xoquox/esp8266-sesam/static.h

const PROGMEM char static_index_html[] = {
  0x20, 0x3c, 0x21, 0x44, 0x4f, 0x43, 0x54, 0x59, 0x50, 0x45, 0x20, 0x68,
  0x74, 0x6d, 0x6c, 0x3e, 0x0a, 0x20, 0x3c, 0x68, 0x74, 0x6d, 0x6c, 0x20,
  0x6c, 0x61, 0x6e, 0x67, 0x3d, 0x22, 0x65, 0x6e, 0x22, 0x3e, 0x0a, 0x20,
  0x3c, 0x68, 0x65, 0x61, 0x64, 0x3e, 0x0a, 0x20, 0x3c, 0x6d, 0x65, 0x74,
  0x61, 0x20, 0x63, 0x68, 0x61, 0x72, 0x73, 0x65, 0x74, 0x3d, 0x22, 0x75,
  0x74, 0x66, 0x2d, 0x38, 0x22, 0x3e, 0x0a, 0x20, 0x3c, 0x6d, 0x65, 0x74,
  0x61, 0x20, 0x68, 0x74, 0x74, 0x70, 0x2d, 0x65, 0x71, 0x75, 0x69, 0x76,
  0x3d, 0x22, 0x58, 0x2d, 0x55, 0x41, 0x2d, 0x43, 0x6f, 0x6d, 0x70, 0x61,
  0x74, 0x69, 0x62, 0x6c, 0x65, 0x22, 0x20, 0x63, 0x6f, 0x6e, 0x74, 0x65,
  0x6e, 0x74, 0x3d, 0x22, 0x49, 0x45, 0x3d, 0x65, 0x64, 0x67, 0x65, 0x22,
  0x3e, 0x0a, 0x20, 0x3c, 0x6d, 0x65, 0x74, 0x61, 0x20, 0x6e, 0x61, 0x6d,
  0x65, 0x3d, 0x22, 0x76, 0x69, 0x65, 0x77, 0x70, 0x6f, 0x72, 0x74, 0x22,
  0x20, 0x63, 0x6f, 0x6e, 0x74, 0x65, 0x6e, 0x74, 0x3d, 0x22, 0x77, 0x69,
  0x64, 0x74, 0x68, 0x3d, 0x64, 0x65, 0x76, 0x69, 0x63, 0x65, 0x2d, 0x77,
  0x69, 0x64, 0x74, 0x68, 0x2c, 0x20, 0x69, 0x6e, 0x69, 0x74, 0x69, 0x61,
  0x6c, 0x2d, 0x73, 0x63, 0x61, 0x6c, 0x65, 0x3d, 0x31, 0x22, 0x3e, 0x0a,
  0x20, 0x0a, 0x20, 0x3c, 0x74, 0x69, 0x74, 0x6c, 0x65, 0x3e, 0x53, 0x65,
  0x73, 0x61, 0x6d, 0x2c, 0x20, 0xc3, 0xb6, 0x66, 0x66, 0x6e, 0x65, 0x20,
  0x64, 0x69, 0x63, 0x68, 0x21, 0x3c, 0x2f, 0x74, 0x69, 0x74, 0x6c, 0x65,
  0x3e, 0x0a, 0x20, 0x0a, 0x20, 0x3c, 0x73, 0x74, 0x79, 0x6c, 0x65, 0x20,
  0x74, 0x79, 0x70, 0x65, 0x3d, 0x22, 0x74, 0x65, 0x78, 0x74, 0x2f, 0x63,
  0x73, 0x73, 0x22, 0x3e, 0x0a, 0x20, 0x0a, 0x20, 0x2a, 0x20, 0x7b, 0x0a,
  0x20, 0x66, 0x6f, 0x6e, 0x74, 0x2d, 0x66, 0x61, 0x6d, 0x69, 0x6c, 0x79,
  0x3a, 0x20, 0x22, 0x48, 0x65, 0x6c, 0x76, 0x65, 0x74, 0x69, 0x63, 0x61,
  0x20, 0x4e, 0x65, 0x75, 0x65, 0x22, 0x2c, 0x20, 0x48, 0x65, 0x6c, 0x76,
  0x65, 0x74, 0x69, 0x63, 0x61, 0x2c, 0x20, 0x41, 0x72, 0x69, 0x61, 0x6c,
  0x2c, 0x20, 0x73, 0x61, 0x6e, 0x73, 0x2d, 0x73, 0x65, 0x72, 0x69, 0x66,
  0x3b, 0x0a, 0x20, 0x7d, 0x0a, 0x20, 0x0a, 0x20, 0x62, 0x6f, 0x64, 0x79,
  0x2c, 0x20, 0x68, 0x74, 0x6d, 0x6c, 0x20, 0x7b, 0x0a, 0x20, 0x6d, 0x61,
  0x72, 0x67, 0x69, 0x6e, 0x3a, 0x20, 0x30, 0x3b, 0x0a, 0x20, 0x70, 0x61,
  0x64, 0x64, 0x69, 0x6e, 0x67, 0x3a, 0x20, 0x30, 0x3b, 0x0a, 0x20, 0x0a,
  0x20, 0x62, 0x61, 0x63, 0x6b, 0x67, 0x72, 0x6f, 0x75, 0x6e, 0x64, 0x3a,
  0x20, 0x23, 0x66, 0x39, 0x66, 0x39, 0x66, 0x39, 0x3b, 0x0a, 0x20, 0x7d,
  0x0a, 0x20, 0x0a, 0x20, 0x68, 0x31, 0x20, 0x7b, 0x0a, 0x20, 0x0a, 0x20,
  0x70, 0x61, 0x64, 0x64, 0x69, 0x6e, 0x67, 0x3a, 0x20, 0x32, 0x30, 0x70,
  0x78, 0x3b, 0x0a, 0x20, 0x6d, 0x61, 0x72, 0x67, 0x69, 0x6e, 0x3a, 0x20,
  0x30, 0x3b, 0x0a, 0x20, 0x6d, 0x61, 0x72, 0x67, 0x69, 0x6e, 0x2d, 0x62,
  0x6f, 0x74, 0x74, 0x6f, 0x6d, 0x3a, 0x20, 0x32, 0x30, 0x70, 0x78, 0x3b,
  0x0a, 0x20, 0x0a, 0x20, 0x66, 0x6f, 0x6e, 0x74, 0x2d, 0x73, 0x69, 0x7a,
  0x65, 0x3a, 0x20, 0x31, 0x38, 0x30, 0x25, 0x3b, 0x0a, 0x20, 0x66, 0x6f,
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
unsigned int static_index_html_len = 1709;
